dozencrows/smart-timer/src/util/lcd.h

//=======================================================================
// Copyright Nicholas Tuckett 2015.
// Distributed under the MIT License.
// (See accompanying file license.txt or copy at
//  http://opensource.org/licenses/MIT)
//=======================================================================

/* LCD module header */

#if !defined(__LCD_H__)
#define __LCD_H__

extern void lcdInit();
extern void lcdClear();
extern void lcdSetBacklight(int value);
extern bool lcdIsBacklightOn();
extern void lcdMoveTo(int x, int y);
extern void lcdPuts(const char* s);
extern void lcdPutchar(const char c);
extern void lcdDisplayEnable(int value);

#endif
